E4Force/E4Force-2025/models/Car 3D models (milestones)/IMG-20250404-WA0020.jpeg

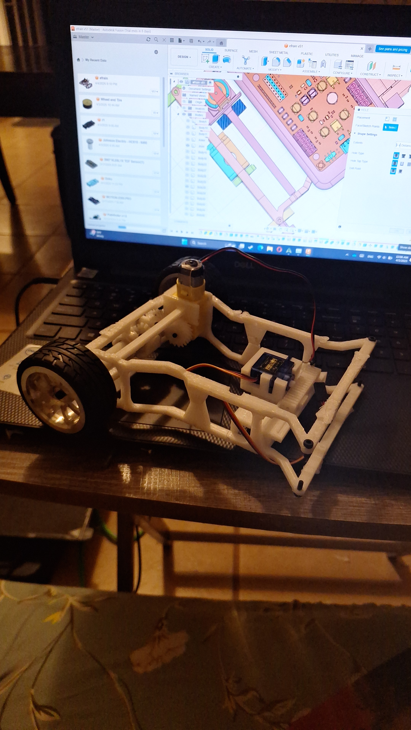
models/Car 3D models (milestones)/IMG-20250404-WA0020.jpeg
