E4Force/E4Force-2025/t-photos/team_picture.jpg

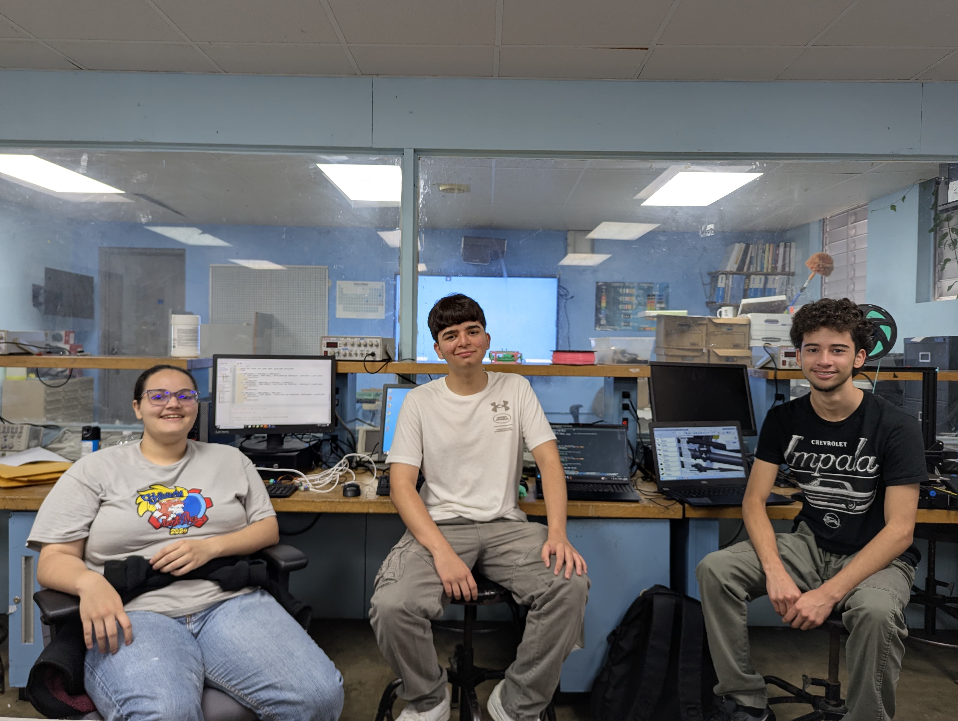
t-photos/team_picture.jpg
