E4Force/E4Force-2025/v-photos/back.jpg

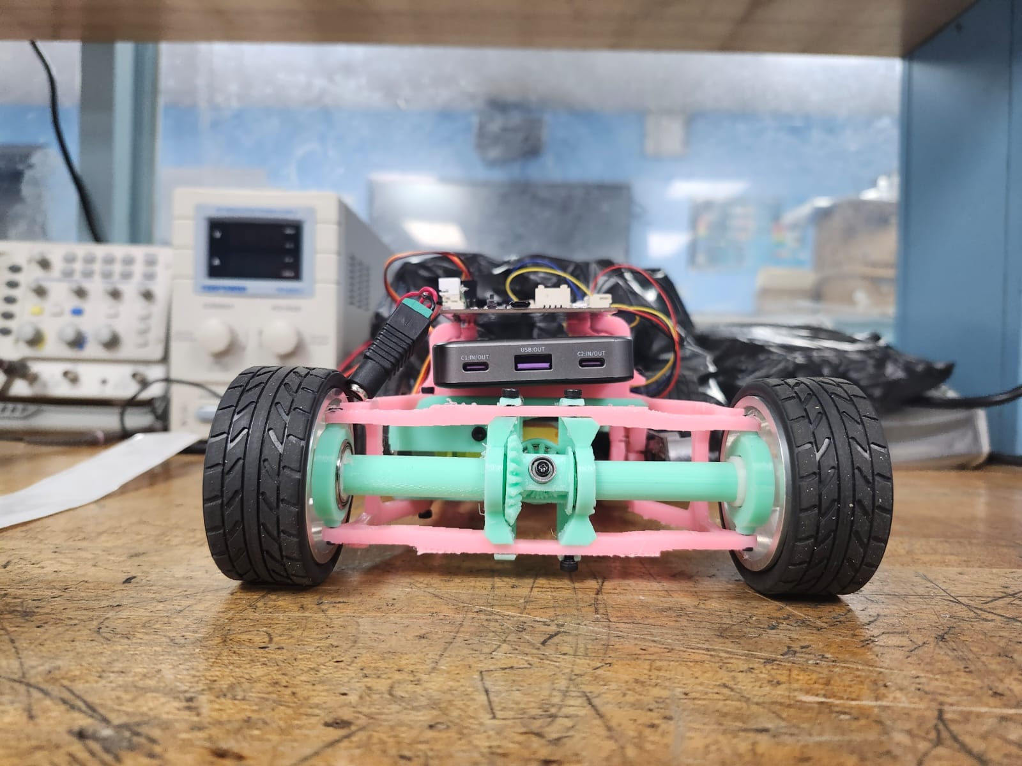
v-photos/back.jpg
