E4Force/E4Force-2025/v-photos/down.jpg

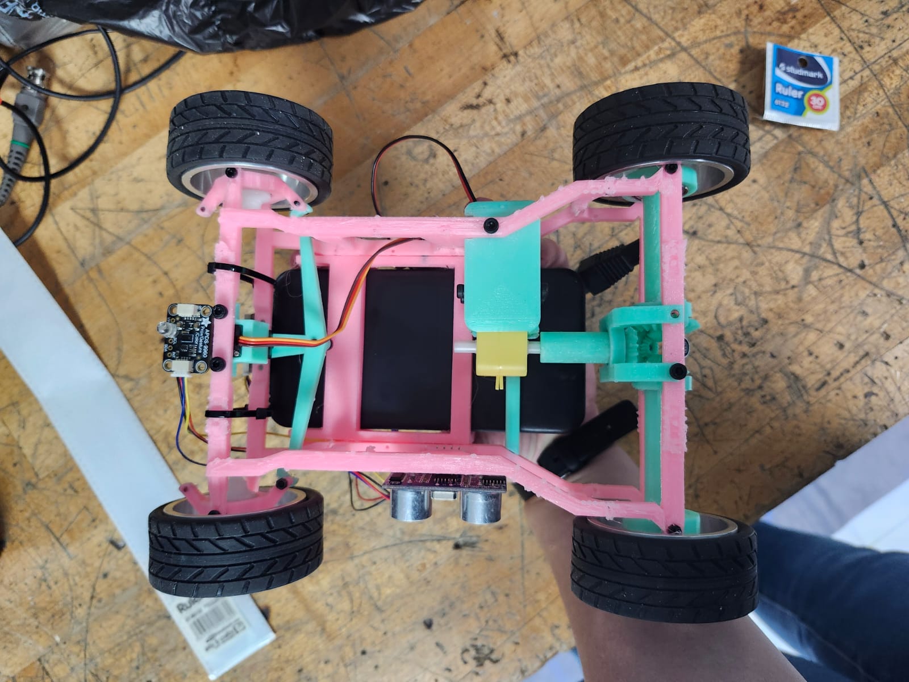
v-photos/down.jpg
