E4Force/E4Force-2025/v-photos/front.jpg

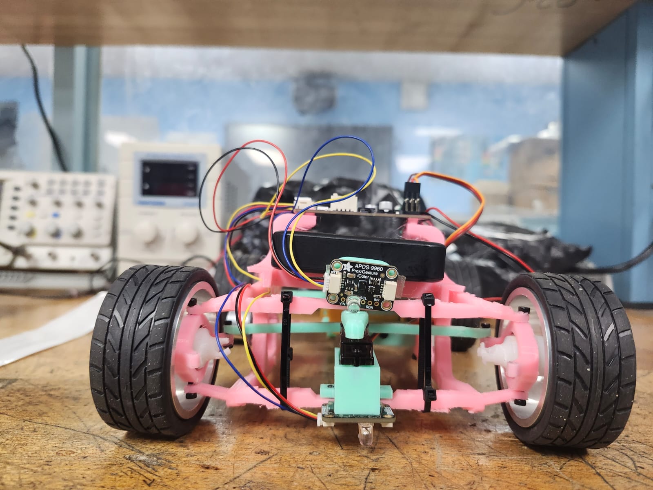
v-photos/front.jpg
