E4Force/E4Force-2025/v-photos/V1_car/20250405_082759.jpg

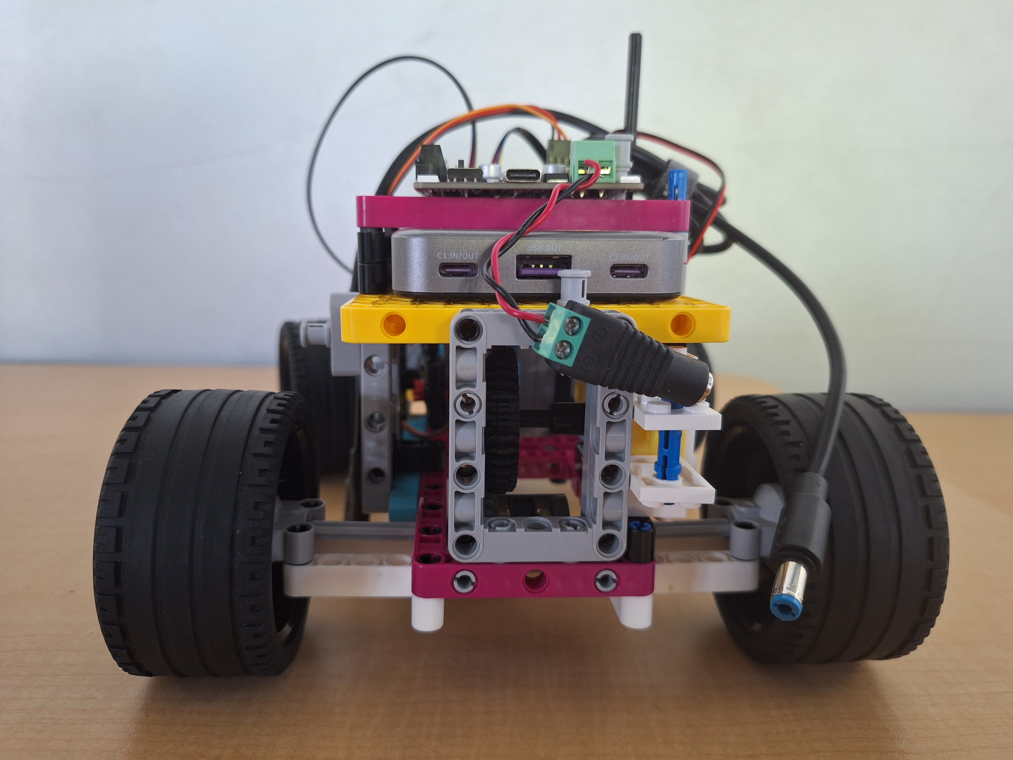
v-photos/V1_car/20250405_082759.jpg
